tebl/C64-Joystick-Adapter/gallery/2021-02-26 02.01.26.jpg

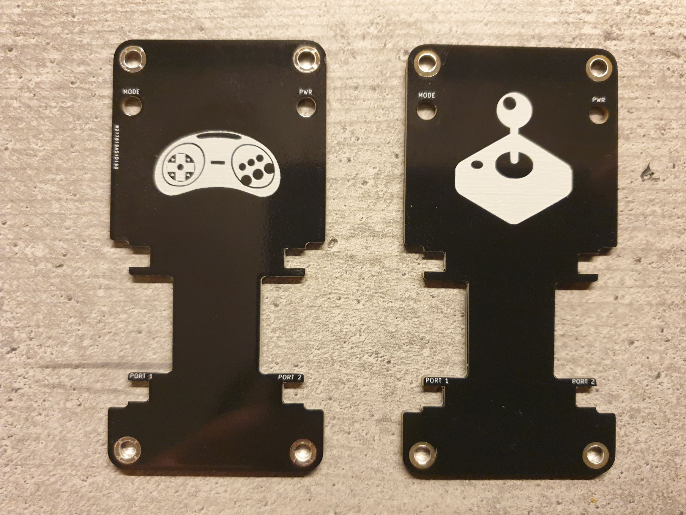
gallery/2021-02-26 02.01.26.jpg
