tebl/C64-Joystick-Adapter/gallery/2021-03-14 21.28.25.jpg

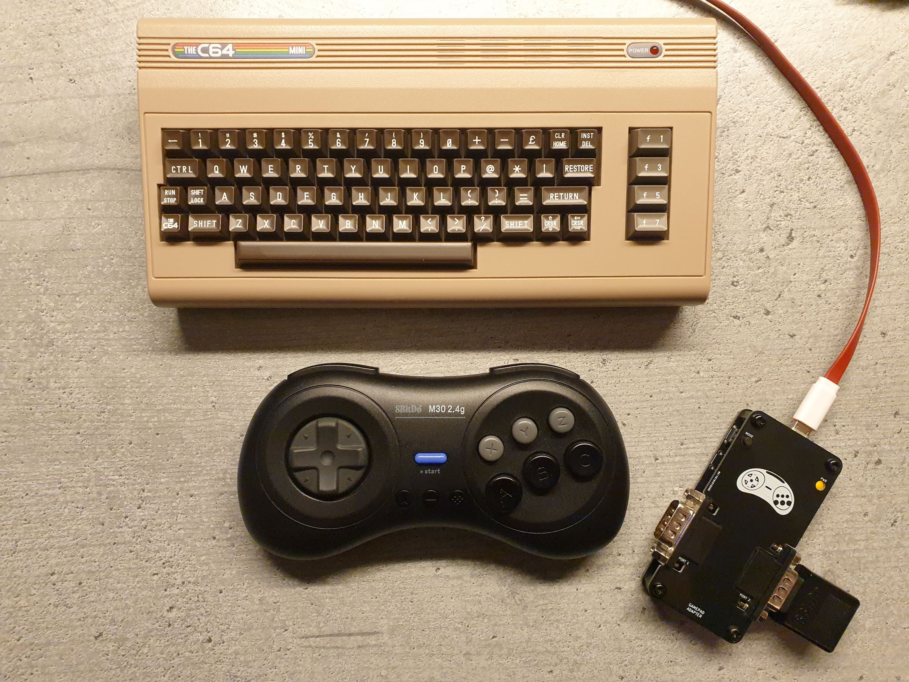
gallery/2021-03-14 21.28.25.jpg
