tebl/C64-Joystick-Adapter/gallery/2022-02-21 23.18.16.jpg

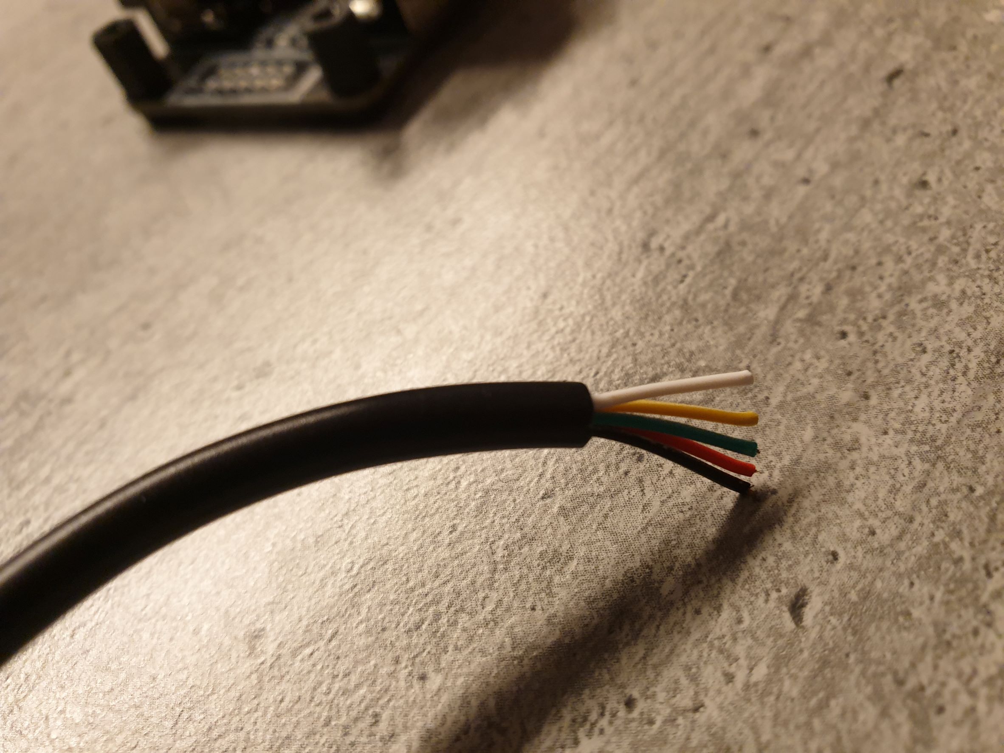
gallery/2022-02-21 23.18.16.jpg
