tebl/C64-Joystick-Adapter/gallery/2022-02-21 23.54.43.jpg

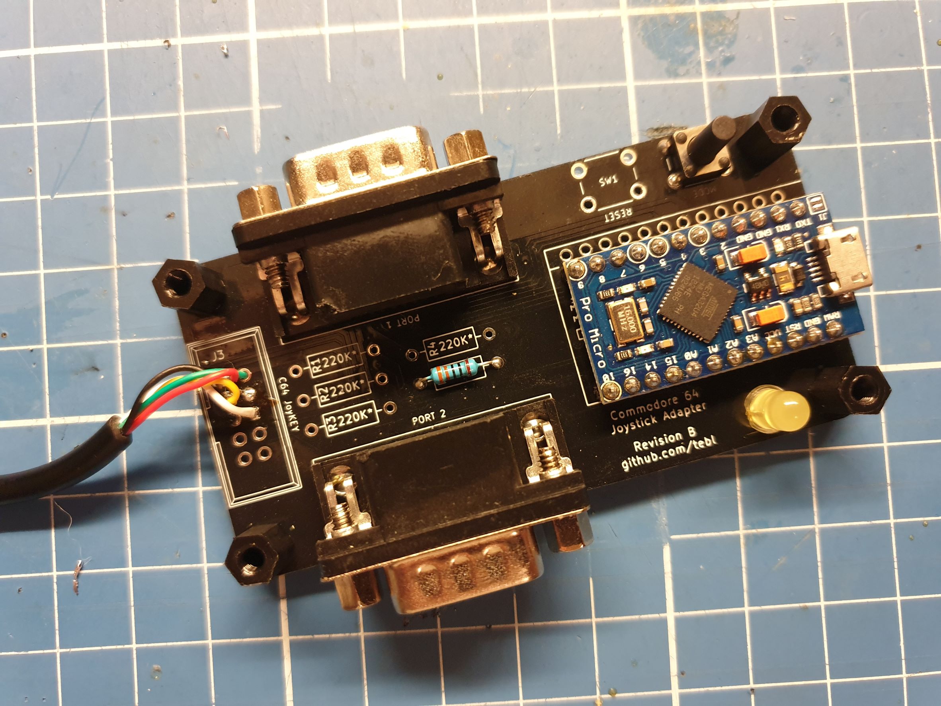
gallery/2022-02-21 23.54.43.jpg
