tebl/C64-Joystick-Adapter/gallery/Preview_revision_B.png

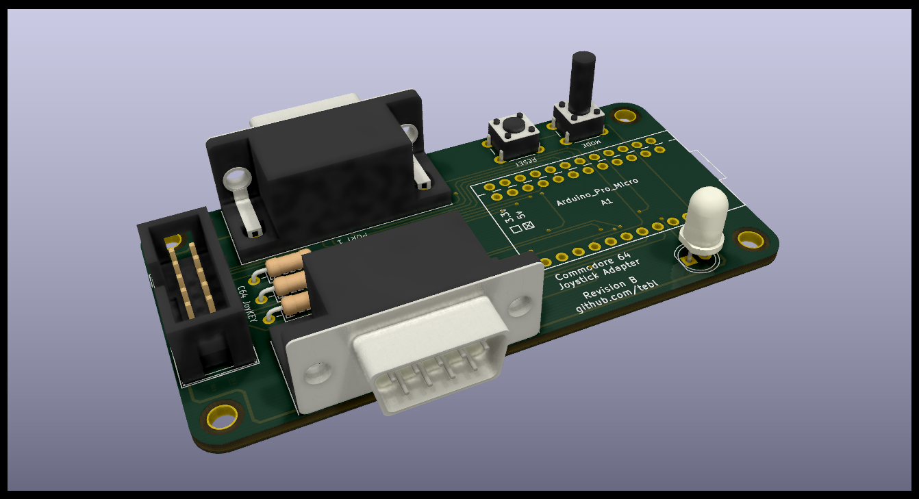
gallery/Preview_revision_B.png
