tebl/C64-Joystick-Adapter/gallery/system_the64.jpg

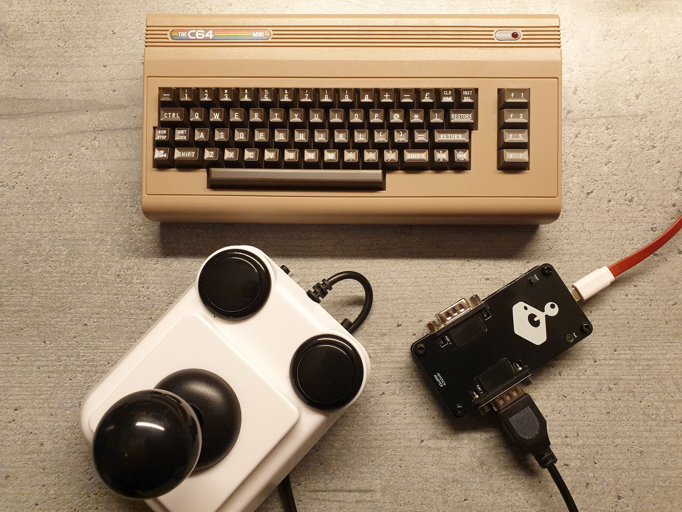
gallery/system_the64.jpg
