tebl/C64-Joystick-Adapter/gallery/system_the64genesis.jpg

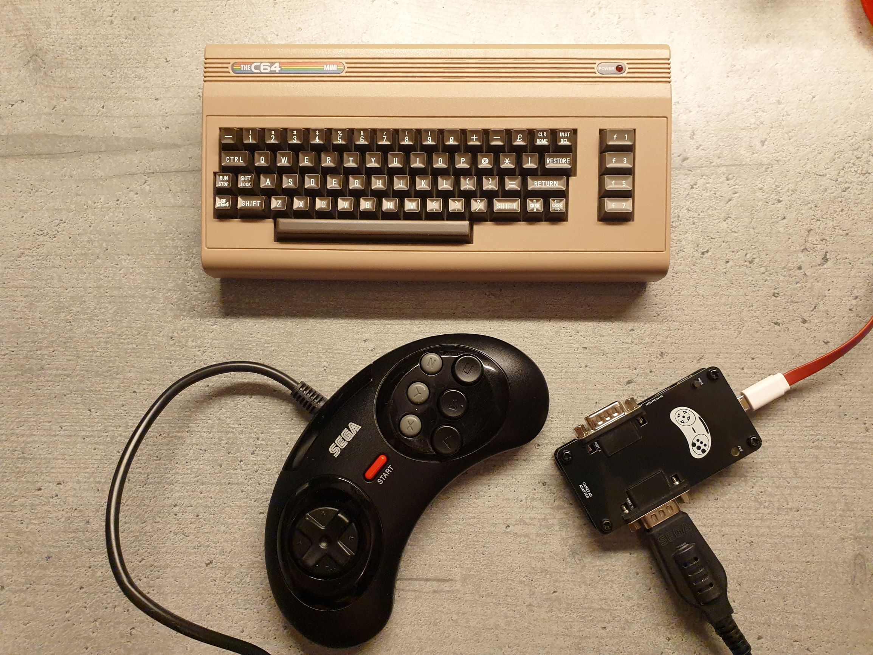
gallery/system_the64genesis.jpg
