tebl/C64-Joystick-Adapter/gallery/system_the64genesis_8bitdo.jpg

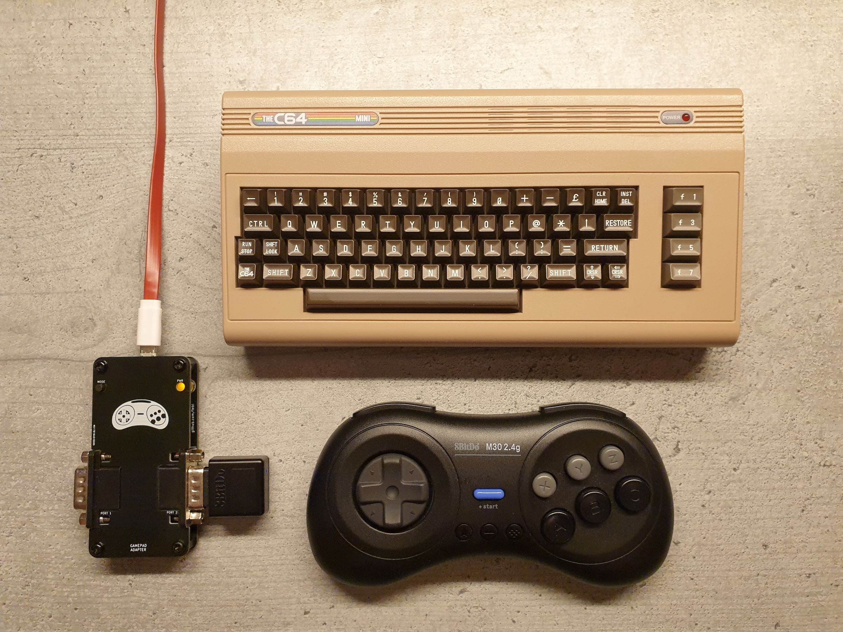
gallery/system_the64genesis_8bitdo.jpg
